ahmedbarakat207/karma/data/maps/floor_1.jpg

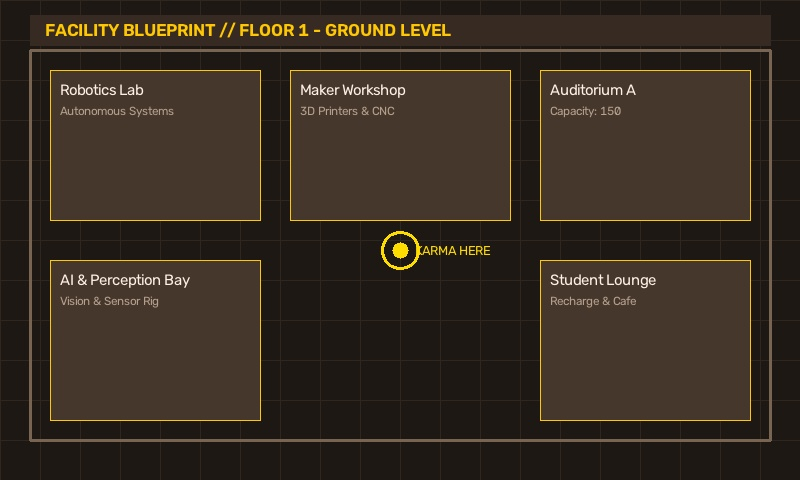
data/maps/floor_1.jpg
