ahmedbarakat207/karma/data/maps/floor_2.jpg

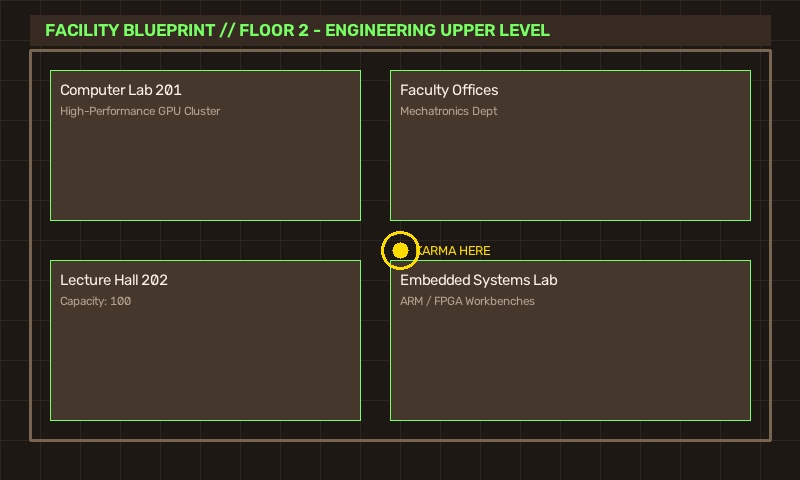
data/maps/floor_2.jpg
